ladyM9/Game_in_C_program/Code/icons.h

#ifndef __ICONS_H__
#define __ICONS_H__

#include <stdint.h>



static const uint16_t image_data_Jagoda[] PROGMEM = {
    0x0000, 0x0000, 0x0000, 0x0000, 0x0000, 0x0000, 0x0000, 0x0000, 0x0000, 0x0000, 0x0000, 0x0000, 0x0000, 0x0000, 0x0000, 0x0000, 0x0000, 0x0000, 
    0x0000, 0x0000, 0x0000, 0x0000, 0x0000, 0x0000, 0x0000, 0x0000, 0x0000, 0x0000, 0x0000, 0x0000, 0x0000, 0x0000, 0x0000, 0x0000, 0x0000, 0x0000, 
    0x0000, 0x0000, 0x0000, 0x0000, 0x0000, 0x0000, 0x0000, 0x0000, 0x0000, 0x0000, 0x0000, 0x0000, 0x0000, 0x0000, 0x0000, 0x0000, 0x0000, 0x0000, 
    0x0000, 0x0000, 0x0000, 0x0000, 0x0000, 0x0000, 0x0000, 0x0000, 0x1208, 0x12cb, 0x32ce, 0x5170, 0x6b30, 0x0020, 0x0000, 0x0000, 0x0000, 0x0000, 
    0x0000, 0x0000, 0x0000, 0x0000, 0x0000, 0x0000, 0x1208, 0x36ba, 0x367a, 0x3659, 0x2e99, 0x8356, 0x7277, 0x6b10, 0x0000, 0x0000, 0x0000, 0x0000, 
    0x0000, 0x0000, 0x0000, 0x0000, 0x0000, 0x1b6d, 0x36db, 0x2cf6, 0x2db7, 0x2df8, 0x2e18, 0x3df8, 0x7a95, 0x6252, 0x1063, 0x0000, 0x0000, 0x0000, 
    0x0000, 0x0000, 0x0000, 0x0000, 0x12cb, 0x36ba, 0x2e18, 0x2e18, 0x2df8, 0x2df8, 0x2df7, 0x6a55, 0x7a95, 0x8357, 0x394b, 0x0000, 0x0000, 0x0000, 
    0x0000, 0x0000, 0x0000, 0x00a2, 0x36db, 0x3618, 0x2495, 0x2e18, 0x2df7, 0x2e18, 0x35d7, 0x5517, 0x4d97, 0x7b36, 0x72d6, 0x0000, 0x0000, 0x0000, 
    0x0000, 0x0000, 0x0000, 0x2d34, 0x2d97, 0x2d56, 0x3618, 0x2df7, 0x2e18, 0x2495, 0x2e18, 0x2e18, 0x2678, 0x82d5, 0x8319, 0x4a6b, 0x0000, 0x0000, 
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
};
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
