ladyM9/Game_in_C_program/Code/lab.h

#ifndef __LAB_H__ 
#define __LAB_H__ 
#include "myDefines.h" 
#include "ILI9341_STM32.h" 
const myline_t lab1Lines[] = {{3, 5, 128, 5}, {159, 5, 315, 5}, {3, 46, 66, 46}, {97, 46, 159, 46}, {190, 46, 283, 46}, {35, 88, 128, 88}, {159, 88, 190, 88}, {221, 88, 252, 88}, {128, 130, 159, 130}, {190, 130, 283, 130}, {66, 172, 97, 172}, {159, 172, 221, 172}, {3, 213, 159, 213}, {190, 213, 315, 213}, {3, 5, 3, 213}, {35, 88, 35, 172}, {66, 130, 66, 213}, {97, 88, 97, 130}, {128, 46, 128, 88}, {128, 172, 128, 213}, {159, 5, 159, 46}, {159, 88, 159, 213}, {190, 46, 190, 88}, {221, 88, 221, 130}, {252, 130, 252, 213}, {283, 46, 283, 88}, {283, 130, 283, 172}, {315, 5, 315, 213}};
const myMaze_t lab1 = {(myline_t*)lab1Lines ,143 , 5  , {159, 213, 190, 213 },sizeof(lab1Lines) / sizeof(myline_t)};
const myline_t lab2Lines[] = {{3, 5, 128, 5}, {159, 5, 315, 5}, {97, 46, 221, 46}, {252, 46, 283, 46}, {35, 88, 128, 88}, {159, 88, 252, 88}, {128, 130, 190, 130}, {97, 172, 128, 172}, {190, 172, 283, 172}, {3, 213, 159, 213}, {190, 213, 315, 213}, {3, 5, 3, 213}, {35, 46, 35, 88}, {35, 130, 35, 213}, {66, 5, 66, 46}, {66, 88, 66, 172}, {97, 130, 97, 213}, {128, 46, 128, 88}, {159, 130, 159, 213}, {190, 88, 190, 130}, {190, 172, 190, 213}, {221, 46, 221, 88}, {221, 130, 221, 172}, {252, 88, 252, 130}, {283, 46, 283, 172}, {315, 5, 315, 213}};
const myMaze_t lab2 = {(myline_t*)lab2Lines ,143 , 5  , {159, 213, 190, 213 },sizeof(lab2Lines) / sizeof(myline_t)};
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
7, 301, 102}, {301, 174, 301, 202}, {317, 1, 317, 217}};
const myMaze_t lab11 = {(myline_t*)lab11Lines ,151 , 1  , {159, 217, 175, 217 },sizeof(lab11Lines) / sizeof(myline_t)};
const myline_t lab12Lines[] = {{1, 1, 143, 1}, {159, 1, 317, 1}, {17, 16, 33, 16}, {80, 16, 127, 16}, {159, 16, 175, 16}, {238, 16, 269, 16}, {285, 16, 301, 16}, {1, 30, 17, 30}, {49, 30, 64, 30}, {80, 30, 96, 30}, {159, 30, 222, 30}, {269, 30, 285, 30}, {17, 44, 49, 44}, {64, 44, 80, 44}, {112, 44, 127, 44}, {159, 44, 191, 44}, {222, 44, 269, 44}, {285, 44, 301, 44}, {33, 59, 112, 59}, {127, 59, 175, 59}, {191, 59, 238, 59}, {269, 59, 285, 59}, {17, 73, 64, 73}, {112, 73, 159, 73}, {175, 73, 222, 73}, {238, 73, 254, 73}, {269, 73, 317, 73}, {1, 87, 17, 87}, {49, 87, 80, 87}, {96, 87, 127, 87}, {143, 87, 159, 87}, {222, 87, 301, 87}, {1, 102, 64, 102}, {96, 102, 112, 102}, {127, 102, 175, 102}, {238, 102, 269, 102}, {17, 116, 96, 116}, {112, 116, 143, 116}, {175, 116, 191, 116}, {206, 116, 238, 116}, {254, 116, 301, 116}, {80, 131, 112, 131}, {143, 131, 159, 131}, {191, 131, 206, 131}, {301, 131, 317, 131}, {17, 145, 33, 145}, {64, 145, 96, 145}, {159, 145, 191, 145}, {206, 145, 222, 145}, {238, 145, 301, 145}, {1, 159, 17, 159}, {33, 159, 64, 159}, {80, 159, 112, 159}, {143, 159, 159, 159}, {191, 159, 206, 159}, {238, 159, 254, 159}, {269, 159, 317, 159}, {17, 174, 33, 174}, {64, 174, 80, 174}, {143, 174, 159, 174}, {191, 174, 238, 174}, {1, 188, 17, 188}, {33, 188, 143, 188}, {159, 188, 175, 188}, {191, 188, 254, 188}, {17, 202, 64, 202}, {112, 202, 127, 202}, {143, 202, 159, 202}, {206, 202, 238, 202}, {254, 202, 301, 202}, {1, 217, 159, 217}, {175, 217, 317, 217}, {1, 1, 1, 217}, {17, 44, 17, 73}, {17, 116, 17, 131}, {17, 145, 17, 159}, {33, 16, 33, 44}, {33, 87, 33, 102}, {33, 131, 33, 145}, {33, 159, 33, 174}, {33, 188, 33, 202}, {49, 1, 49, 16}, {49, 30, 49, 44}, {49, 116, 49, 131}, {49, 145, 49, 159}, {49, 174, 49, 188}, {64, 1, 64, 30}, {64, 44, 64, 59}, {64, 116, 64, 174}, {80, 30, 80, 44}, {80, 59, 80, 116}, {80, 202, 80, 217}, {96, 16, 96, 30}, {96, 44, 96, 59}, {96, 73, 96, 87}, {96, 159, 96, 202}, {112, 30, 112, 44}, {112, 59, 112, 73}, {112, 102, 112, 174}, {112, 202, 112, 217}, {127, 16, 127, 59}, {127, 87, 127, 102}, {127, 116, 127, 174}, {143, 1, 143, 44}, {143, 131, 143, 159}, {143, 174, 143, 202}, {159, 16, 159, 30}, {159, 73, 159, 87}, {159, 102, 159, 131}, {159, 159, 159, 174}, {159, 202, 159, 217}, {175, 59, 175, 102}, {175, 116, 175, 217}, {191, 1, 191, 16}, {191, 44, 191, 59}, {191, 87, 191, 116}, {191, 145, 191, 159}, {191, 188, 191, 202}, {206, 16, 206, 30}, {206, 44, 206, 59}, {206, 73, 206, 145}, {206, 159, 206, 174}, {222, 1, 222, 44}, {222, 87, 222, 116}, {222, 131, 222, 159}, {238, 16, 238, 30}, {238, 59, 238, 73}, {238, 116, 238, 145}, {238, 159, 238, 174}, {238, 202, 238, 217}, {254, 30, 254, 59}, {254, 73, 254, 87}, {254, 116, 254, 131}, {254, 159, 254, 202}, {269, 16, 269, 44}, {269, 59, 269, 73}, {269, 87, 269, 102}, {269, 131, 269, 145}, {269, 159, 269, 188}, {285, 1, 285, 16}, {285, 44, 285, 59}, {285, 102, 285, 145}, {285, 159, 285, 174}, {285, 188, 285, 202}, {301, 16, 301, 30}, {301, 59, 301, 73}, {301, 87, 301, 102}, {301, 174, 301, 202}, {317, 1, 317, 217}};
const myMaze_t lab12 = {(myline_t*)lab12Lines ,151 , 1  , {159, 217, 175, 217 },sizeof(lab12Lines) / sizeof(myline_t)};
const myline_t lab13Lines[] = {{1, 1, 143, 1}, {159, 1, 317, 1}, {17, 16, 49, 16}, {96, 16, 159, 16}, {206, 16, 238, 16}, {254, 16, 269, 16}, {1, 30, 33, 30}, {49, 30, 64, 30}, {191, 30, 222, 30}, {238, 30, 254, 30}, {285, 30, 317, 30}, {64, 44, 127, 44}, {222, 44, 254, 44}, {269, 44, 301, 44}, {49, 59, 64, 59}, {127, 59, 238, 59}, {254, 59, 317, 59}, {33, 73, 80, 73}, {112, 73, 127, 73}, {159, 73, 222, 73}, {285, 73, 301, 73}, {17, 87, 33, 87}, {64, 87, 112, 87}, {159, 87, 191, 87}, {269, 87, 285, 87}, {301, 87, 317, 87}, {33, 102, 49, 102}, {64, 102, 80, 102}, {112, 102, 127, 102}, {143, 102, 159, 102}, {191, 102, 238, 102}, {254, 102, 269, 102}, {17, 116, 33, 116}, {49, 116, 64, 116}, {112, 116, 127, 116}, {143, 116, 175, 116}, {191, 116, 206, 116}, {222, 116, 254, 116}, {269, 116, 285, 116}, {49, 131, 112, 131}, {127, 131, 143, 131}, {175, 131, 191, 131}, {206, 131, 222, 131}, {254, 131, 269, 131}, {285, 131, 301, 131}, {64, 145, 80, 145}, {143, 145, 191, 145}, {269, 145, 317, 145}, {17, 159, 33, 159}, {80, 159, 96, 159}, {127, 159, 143, 159}, {222, 159, 238, 159}, {269, 159, 301, 159}, {1, 174, 17, 174}, {33, 174, 64, 174}, {112, 174, 127, 174}, {143, 174, 175, 174}, {238, 174, 269, 174}, {285, 174, 317, 174}, {64, 188, 112, 188}, {127, 188, 143, 188}, {175, 188, 191, 188}, {269, 188, 285, 188}, {143, 202, 175, 202}, {191, 202, 206, 202}, {238, 202, 269, 202}, {285, 202, 301, 202}, {1, 217, 159, 217}, {175, 217, 317, 217}, {1, 1, 1, 217}, {17, 44, 17, 102}, {17, 116, 17, 159}, {17, 174, 17, 202}, {33, 30, 33, 73}, {33, 87, 33, 116}, {33, 131, 33, 202}, {49, 1, 49, 16}, {49, 30, 49, 59}, {49, 73, 49, 87}, {49, 102, 49, 159}, {49, 174, 49, 202}, {64, 16, 64, 30}, {64, 44, 64, 59}, {64, 87, 64, 102}, {64, 145, 64, 174}, {64, 202, 64, 217}, {80, 16, 80, 44}, {80, 59, 80, 73}, {80, 102, 80, 116}, {80, 159, 80, 202}, {96, 16, 96, 30}, {96, 44, 96, 131}, {96, 145, 96, 174}, {96, 202, 96, 217}, {112, 30, 112, 44}, {112, 59, 112, 73}, {112, 102, 112, 116}, {112, 131, 112, 202}, {127, 16, 127, 30}, {127, 44, 127, 59}, {127, 73, 127, 102}, {127, 116, 127, 159}, {127, 174, 127, 217}, {143, 30, 143, 116}, {143, 159, 143, 174}, {159, 1, 159, 44}, {159, 73, 159, 87}, {159, 116, 159, 131}, {159, 145, 159, 159}, {159, 174, 159, 202}, {175, 16, 175, 59}, {175, 102, 175, 116}, {175, 131, 175, 145}, {175, 159, 175, 174}, {175, 202, 175, 217}, {191, 16, 191, 44}, {191, 87, 191, 131}, {191, 145, 191, 188}, {206, 1, 206, 16}, {206, 44, 206, 59}, {206, 73, 206, 87}, {206, 131, 206, 202}, {222, 30, 222, 44}, {222, 87, 222, 131}, {222, 145, 222, 217}, {238, 16, 238, 30}, {238, 44, 238, 87}, {238, 131, 238, 159}, {238, 188, 238, 202}, {254, 1, 254, 16}, {254, 73, 254, 188}, {269, 16, 269, 44}, {269, 59, 269, 102}, {269, 116, 269, 131}, {269, 159, 269, 174}, {269, 188, 269, 202}, {285, 16, 285, 30}, {285, 73, 285, 87}, {285, 102, 285, 116}, {285, 131, 285, 145}, {285, 174, 285, 188}, {285, 202, 285, 217}, {301, 1, 301, 16}, {301, 102, 301, 131}, {301, 188, 301, 202}, {317, 1, 317, 217}};
const myMaze_t lab13 = {(myline_t*)lab13Lines ,151 , 1  , {159, 217, 175, 217 },sizeof(lab13Lines) / sizeof(myline_t)};
#endif
